ricklon/attinyservo/programming/ProgrammingAttinyServoFromArduino.png

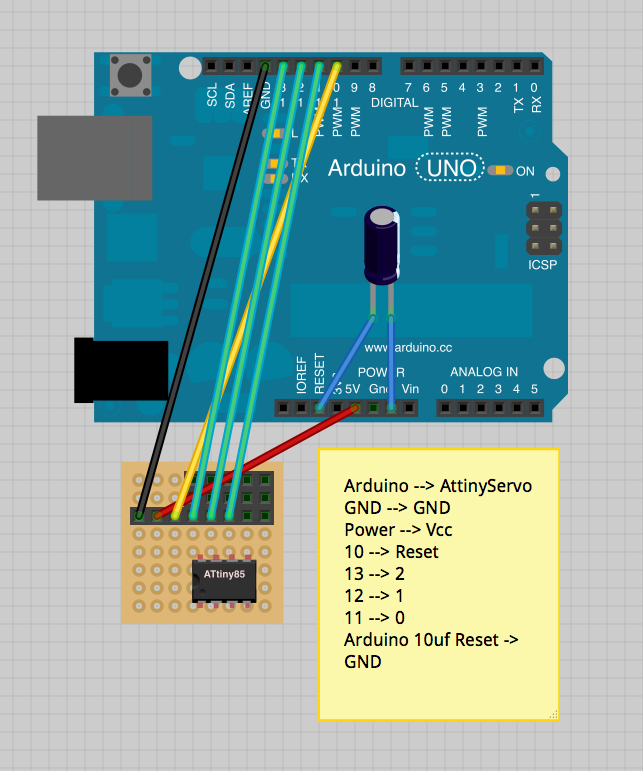
programming/ProgrammingAttinyServoFromArduino.png
