ricklon/attinyservo/programming/QRForProgrammingSite.png

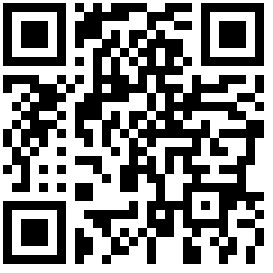
programming/QRForProgrammingSite.png
