ricklon/attinyservo/programming/QRProjectSite.png

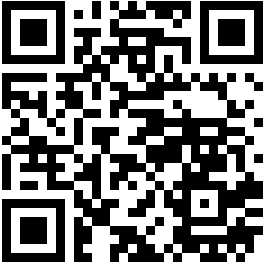
programming/QRProjectSite.png
