ricklon/attinyservo/pth/images/Attinyservo1.1_pth.png

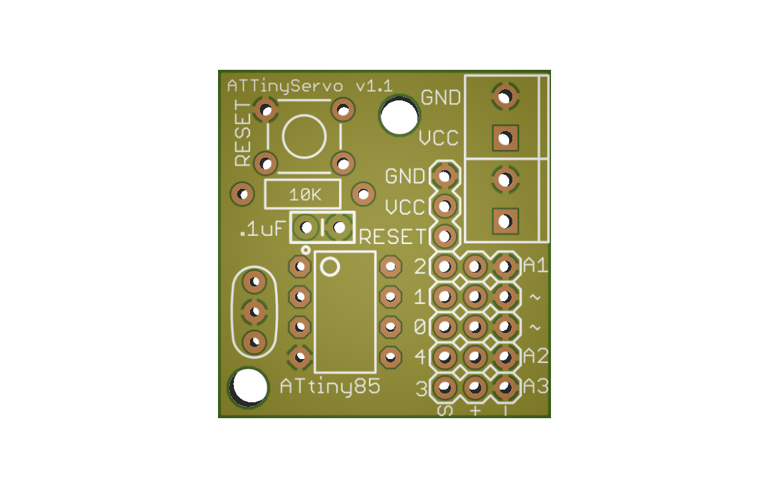
pth/images/Attinyservo1.1_pth.png
