ricklon/attinyservo/smt/images/AttinyServo1_0_smt.png

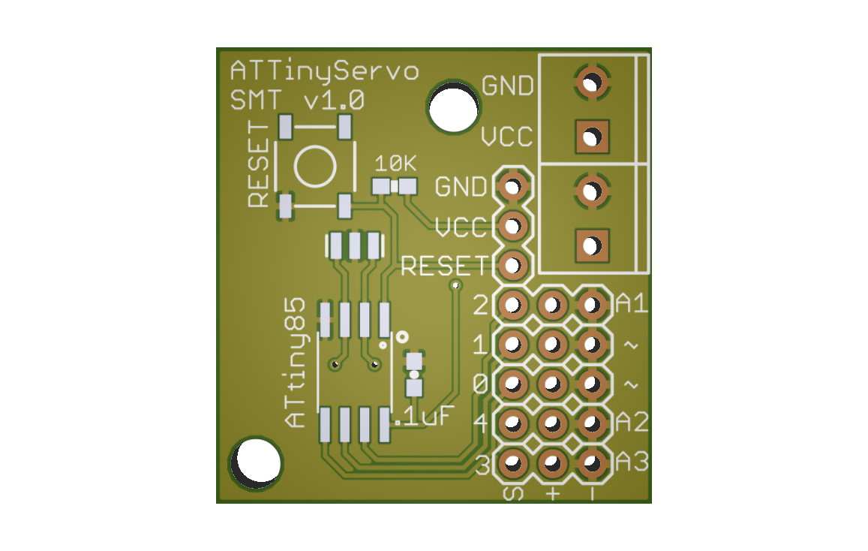
smt/images/AttinyServo1_0_smt.png
