ricklon/attinyservo/smt/schematic/eagleUp/eagleUp_ATTinyServoSMT_v10_bottom_mask.png

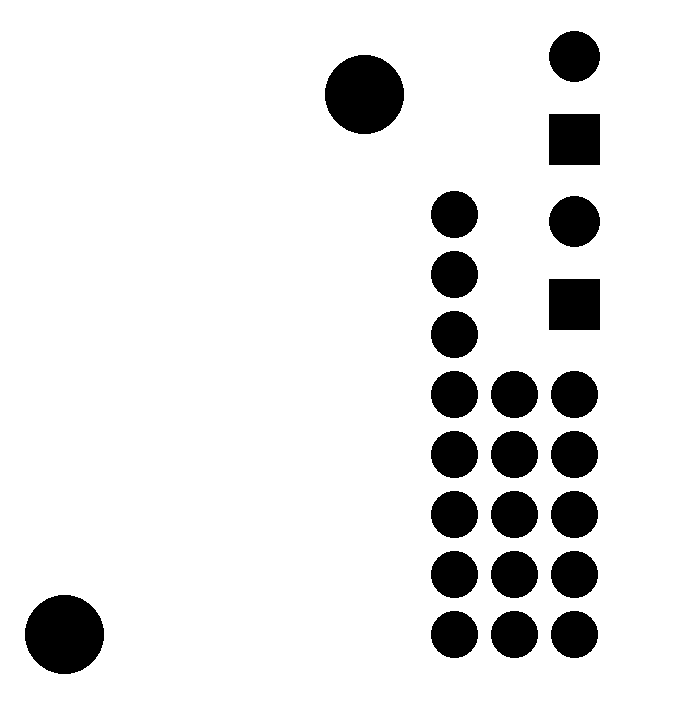
smt/schematic/eagleUp/eagleUp_ATTinyServoSMT_v10_bottom_mask.png
